technomancer-lv/usb-current-loop-converter/pictures/03-cl-interface-bot.jpg

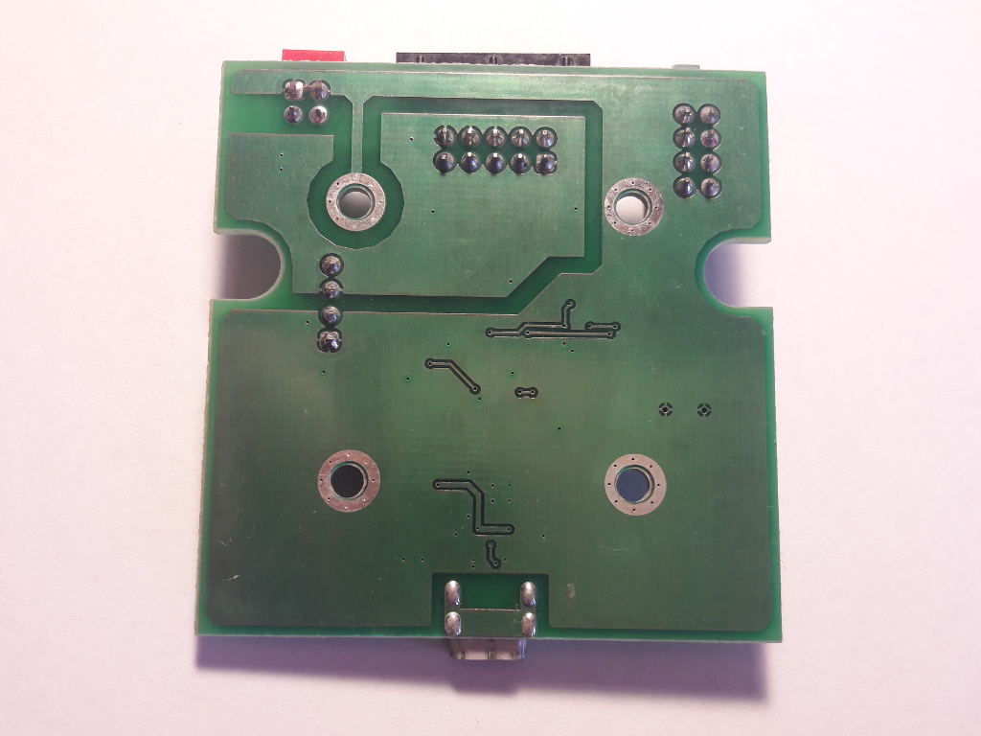
pictures/03-cl-interface-bot.jpg
